stanoba/oblatkovac/Software/src/config.h

// ############################  Static Variables  #############################

const double hysteresis = 0.5;
const int default_temp = 134; // 134
const int min_temp = 100; // 100
const int max_temp = 160; // 160
const int default_time = 30; // 30
const int min_time = 10;
const int max_time = 90;
#define DEBUG 0 // Set to 1 to enable debug output via Serial
